Choccy-vr/BeanPad/Project Images/Screenshot 2025-06-17 155903.png

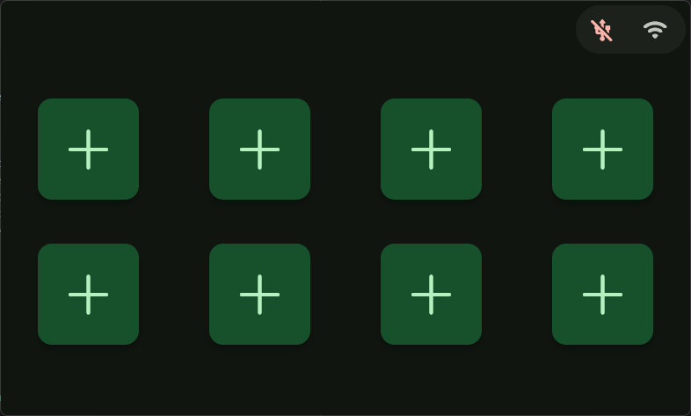
Project Images/Screenshot 2025-06-17 155903.png
